tqlabs-in/dimled-mark-2/output/images/DimLED.png

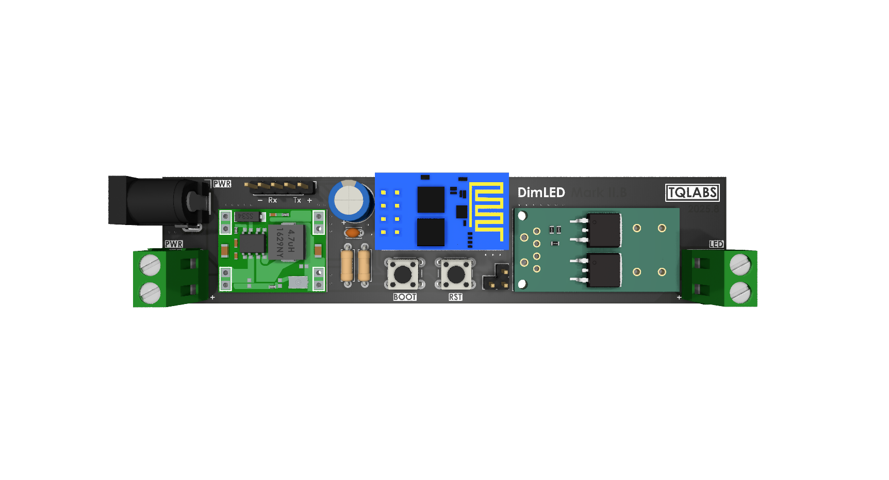
output/images/DimLED.png
